mihaelazaluceanu/eBook-reader/Images/Dispozitiv Final Front.jpg

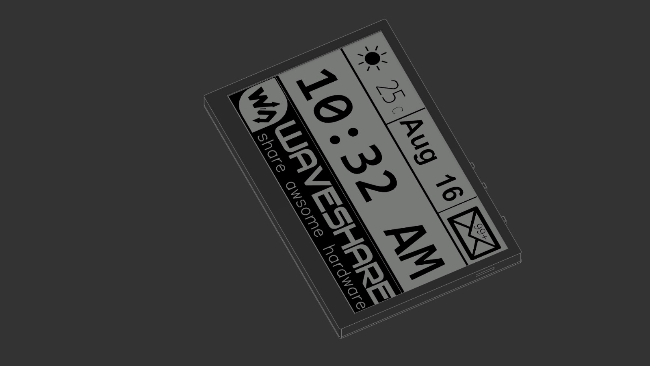
Images/Dispozitiv Final Front.jpg
